Klackygears/eek_doc/eek_pcb/eek.kicad_sch

## KiCad design eek_pcb/eek.kicad_sch (2022-06-14)

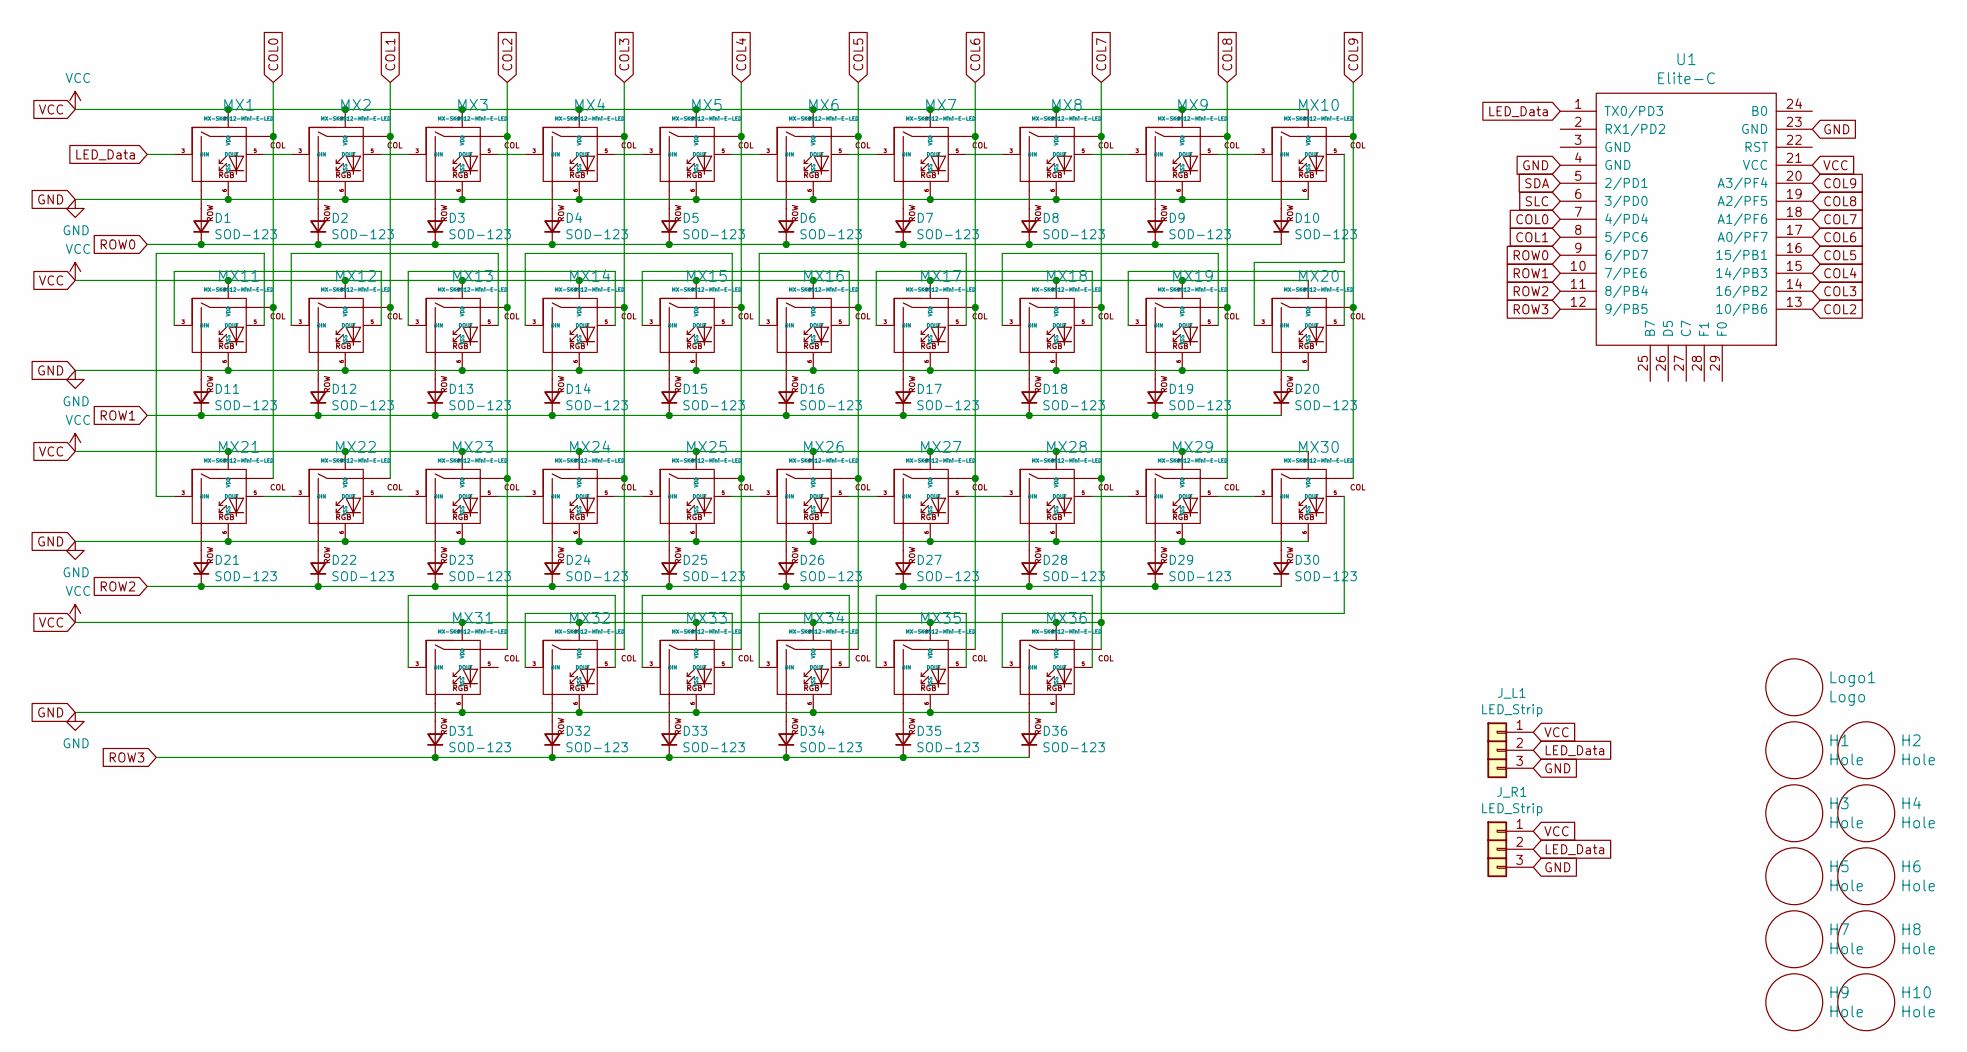
[picture p15: schematic eek.kicad_sch]

Parts:
D1, D2, D3, D4, D5, D6, D7, D8, D9, D10, D11, D12, D13, D14, D15, D16, D17, D18, D19, D20, D21, D22, D23, D24, D25, D26, D27, D28, D29, D30, D31, D32, D33, D34, D35, D36: SOD-123; ComboDiode_doublesided
H1, H2, H3, H4, H5, H6, H7, H8, H9, H10: Hole; GearLogo_smallsolder
J_L1: LED_Strip; StripLED
J_R1: LED_Strip; StripLED
Logo1: Logo; GearLogo_smallsolder
MX1, MX2, MX3, MX4, MX5, MX6, MX7, MX8, MX9, MX10, MX11, MX12, MX13, MX14, MX15, MX16, MX17, MX18, MX19, MX20, MX21, MX22, MX23, MX24, MX25, MX26, MX27, MX28, MX29, MX30, MX31, MX32, MX33, MX34, MX35, MX36: MX-SK6812-Mini-E-LED; UnivSwitch_SK6812-Mini-E_RC
U1: Elite-C; Elite-C-castellated-29pin-holes_nobsilk

Connections:
COL0: MX1.1 (COL), MX11.1 (COL), MX21.1 (COL), U1.7 (4/PD4)
COL1: MX2.1 (COL), MX12.1 (COL), MX22.1 (COL), U1.8 (5/PC6)
COL2: MX3.1 (COL), MX13.1 (COL), MX23.1 (COL), MX31.1 (COL), U1.13 (10/PB6)
COL3: MX4.1 (COL), MX14.1 (COL), MX24.1 (COL), MX32.1 (COL), U1.14 (16/PB2)
COL4: MX5.1 (COL), MX15.1 (COL), MX25.1 (COL), MX33.1 (COL), U1.15 (14/PB3)
COL5: MX6.1 (COL), MX16.1 (COL), MX26.1 (COL), MX34.1 (COL), U1.16 (15/PB1)
COL6: MX7.1 (COL), MX17.1 (COL), MX27.1 (COL), MX35.1 (COL), U1.17 (A0/PF7)
COL7: J_L1.1, J_R1.1, MX1.4 (VDD), MX2.4 (VDD), MX3.4 (VDD), MX4.4 (VDD), MX5.4 (VDD), MX6.4 (VDD), MX7.4 (VDD), MX8.1 (COL), MX8.4 (VDD), MX9.4 (VDD), MX10.4 (VDD), MX11.4 (VDD), MX12.4 (VDD), MX13.4 (VDD), MX14.4 (VDD), MX15.4 (VDD), MX16.4 (VDD), MX17.4 (VDD), MX18.1 (COL), MX18.4 (VDD), MX19.4 (VDD), MX20.4 (VDD), MX21.4 (VDD), MX22.4 (VDD), MX23.4 (VDD), MX24.4 (VDD), MX25.4 (VDD), MX26.4 (VDD), MX27.4 (VDD), MX28.1 (COL), MX28.4 (VDD), MX29.4 (VDD), MX30.4 (VDD), MX31.4 (VDD), MX32.4 (VDD), MX33.4 (VDD), MX34.4 (VDD), MX35.4 (VDD), MX36.1 (COL), MX36.4 (VDD), U1.18 (A1/PF6), U1.21 (VCC)
COL8: MX9.1 (COL), MX19.1 (COL), MX29.1 (COL), U1.19 (A2/PF5)
COL9: MX10.1 (COL), MX20.1 (COL), MX30.1 (COL), U1.20 (A3/PF4)
GND: J_L1.3, J_R1.3, MX1.6 (VSS), MX2.6 (VSS), MX3.6 (VSS), MX4.6 (VSS), MX5.6 (VSS), MX6.6 (VSS), MX7.6 (VSS), MX8.6 (VSS), MX9.6 (VSS), MX10.6 (VSS), MX11.6 (VSS), MX12.6 (VSS), MX13.6 (VSS), MX14.6 (VSS), MX15.6 (VSS), MX16.6 (VSS), MX17.6 (VSS), MX18.6 (VSS), MX19.6 (VSS), MX20.6 (VSS), MX21.6 (VSS), MX22.6 (VSS), MX23.6 (VSS), MX24.6 (VSS), MX25.6 (VSS), MX26.6 (VSS), MX27.6 (VSS), MX28.6 (VSS), MX29.6 (VSS), MX30.6 (VSS), MX31.6 (VSS), MX32.6 (VSS), MX33.6 (VSS), MX34.6 (VSS), MX35.6 (VSS), MX36.6 (VSS), U1.4 (GND), U1.23 (GND)
LED_Data: J_L1.2, J_R1.2, MX1.3 (DIN), U1.1 (TX0/PD3)
unnamed: D1.2 (A), MX1.2 (ROW)
unnamed: D2.2 (A), MX2.2 (ROW)
unnamed: D3.2 (A), MX3.2 (ROW)
unnamed: D4.2 (A), MX4.2 (ROW)
unnamed: D5.2 (A), MX5.2 (ROW)
unnamed: D6.2 (A), MX6.2 (ROW)
unnamed: D7.2 (A), MX7.2 (ROW)
unnamed: D8.2 (A), MX8.2 (ROW)
unnamed: D9.2 (A), MX9.2 (ROW)
unnamed: D10.2 (A), MX10.2 (ROW)
unnamed: D11.2 (A), MX11.2 (ROW)
unnamed: D12.2 (A), MX12.2 (ROW)
unnamed: D13.2 (A), MX13.2 (ROW)
unnamed: D14.2 (A), MX14.2 (ROW)
unnamed: D15.2 (A), MX15.2 (ROW)
unnamed: D16.2 (A), MX16.2 (ROW)
unnamed: D17.2 (A), MX17.2 (ROW)
unnamed: D18.2 (A), MX18.2 (ROW)
unnamed: D19.2 (A), MX19.2 (ROW)
unnamed: D20.2 (A), MX20.2 (ROW)
unnamed: D21.2 (A), MX21.2 (ROW)
unnamed: D22.2 (A), MX22.2 (ROW)
unnamed: D23.2 (A), MX23.2 (ROW)
unnamed: D24.2 (A), MX24.2 (ROW)
unnamed: D25.2 (A), MX25.2 (ROW)
unnamed: D26.2 (A), MX26.2 (ROW)
unnamed: D27.2 (A), MX27.2 (ROW)
unnamed: D28.2 (A), MX28.2 (ROW)
unnamed: D29.2 (A), MX29.2 (ROW)
unnamed: D30.2 (A), MX30.2 (ROW)
unnamed: D31.2 (A), MX31.2 (ROW)
unnamed: D32.2 (A), MX32.2 (ROW)
unnamed: D33.2 (A), MX33.2 (ROW)
unnamed: D34.2 (A), MX34.2 (ROW)
unnamed: D35.2 (A), MX35.2 (ROW)
unnamed: D36.2 (A), MX36.2 (ROW)
unnamed: MX1.5 (DOUT), MX2.3 (DIN)
unnamed: MX2.5 (DOUT), MX3.3 (DIN)
unnamed: MX3.5 (DOUT), MX4.3 (DIN)
unnamed: MX4.5 (DOUT), MX5.3 (DIN)
unnamed: MX5.5 (DOUT), MX6.3 (DIN)
unnamed: MX6.5 (DOUT), MX7.3 (DIN)
unnamed: MX7.5 (DOUT), MX8.3 (DIN)
unnamed: MX8.5 (DOUT), MX9.3 (DIN)
unnamed: MX9.5 (DOUT), MX10.3 (DIN)
unnamed: MX10.5 (DOUT), MX20.3 (DIN)
unnamed: MX11.3 (DIN), MX12.5 (DOUT)
unnamed: MX11.5 (DOUT), MX21.3 (DIN)
unnamed: MX12.3 (DIN), MX13.5 (DOUT)
unnamed: MX13.3 (DIN), MX14.5 (DOUT)
unnamed: MX14.3 (DIN), MX15.5 (DOUT)
unnamed: MX15.3 (DIN), MX16.5 (DOUT)
unnamed: MX16.3 (DIN), MX17.5 (DOUT)
unnamed: MX17.3 (DIN), MX18.5 (DOUT)
unnamed: MX18.3 (DIN), MX19.5 (DOUT)
unnamed: MX19.3 (DIN), MX20.5 (DOUT)
unnamed: MX21.5 (DOUT), MX22.3 (DIN)
unnamed: MX22.5 (DOUT), MX23.3 (DIN)
unnamed: MX23.5 (DOUT), MX24.3 (DIN)
unnamed: MX24.5 (DOUT), MX25.3 (DIN)
unnamed: MX25.5 (DOUT), MX26.3 (DIN)
unnamed: MX26.5 (DOUT), MX27.3 (DIN)
unnamed: MX27.5 (DOUT), MX28.3 (DIN)
unnamed: MX28.5 (DOUT), MX29.3 (DIN)
unnamed: MX29.5 (DOUT), MX30.3 (DIN)
unnamed: MX30.5 (DOUT), MX36.3 (DIN)
unnamed: MX31.3 (DIN), MX32.5 (DOUT)
unnamed: MX32.3 (DIN), MX33.5 (DOUT)
unnamed: MX33.3 (DIN), MX34.5 (DOUT)
unnamed: MX34.3 (DIN), MX35.5 (DOUT)
unnamed: MX35.3 (DIN), MX36.5 (DOUT)
ROW0: D1.1 (K), D2.1 (K), D3.1 (K), D4.1 (K), D5.1 (K), D6.1 (K), D7.1 (K), D8.1 (K), D9.1 (K), D10.1 (K), U1.9 (6/PD7)
ROW1: D11.1 (K), D12.1 (K), D13.1 (K), D14.1 (K), D15.1 (K), D16.1 (K), D17.1 (K), D18.1 (K), D19.1 (K), D20.1 (K), U1.10 (7/PE6)
ROW2: D21.1 (K), D22.1 (K), D23.1 (K), D24.1 (K), D25.1 (K), D26.1 (K), D27.1 (K), D28.1 (K), D29.1 (K), D30.1 (K), U1.11 (8/PB4)
ROW3: D31.1 (K), D32.1 (K), D33.1 (K), D34.1 (K), D35.1 (K), D36.1 (K), U1.12 (9/PB5)
SDA: U1.5 (2/PD1)
SLC: U1.6 (3/PD0)
